KoBussLLC/grabert-hardware/PCB/grabert.kicad_sch

## KiCad design PCB/grabert.kicad_sch (2021-04-06)

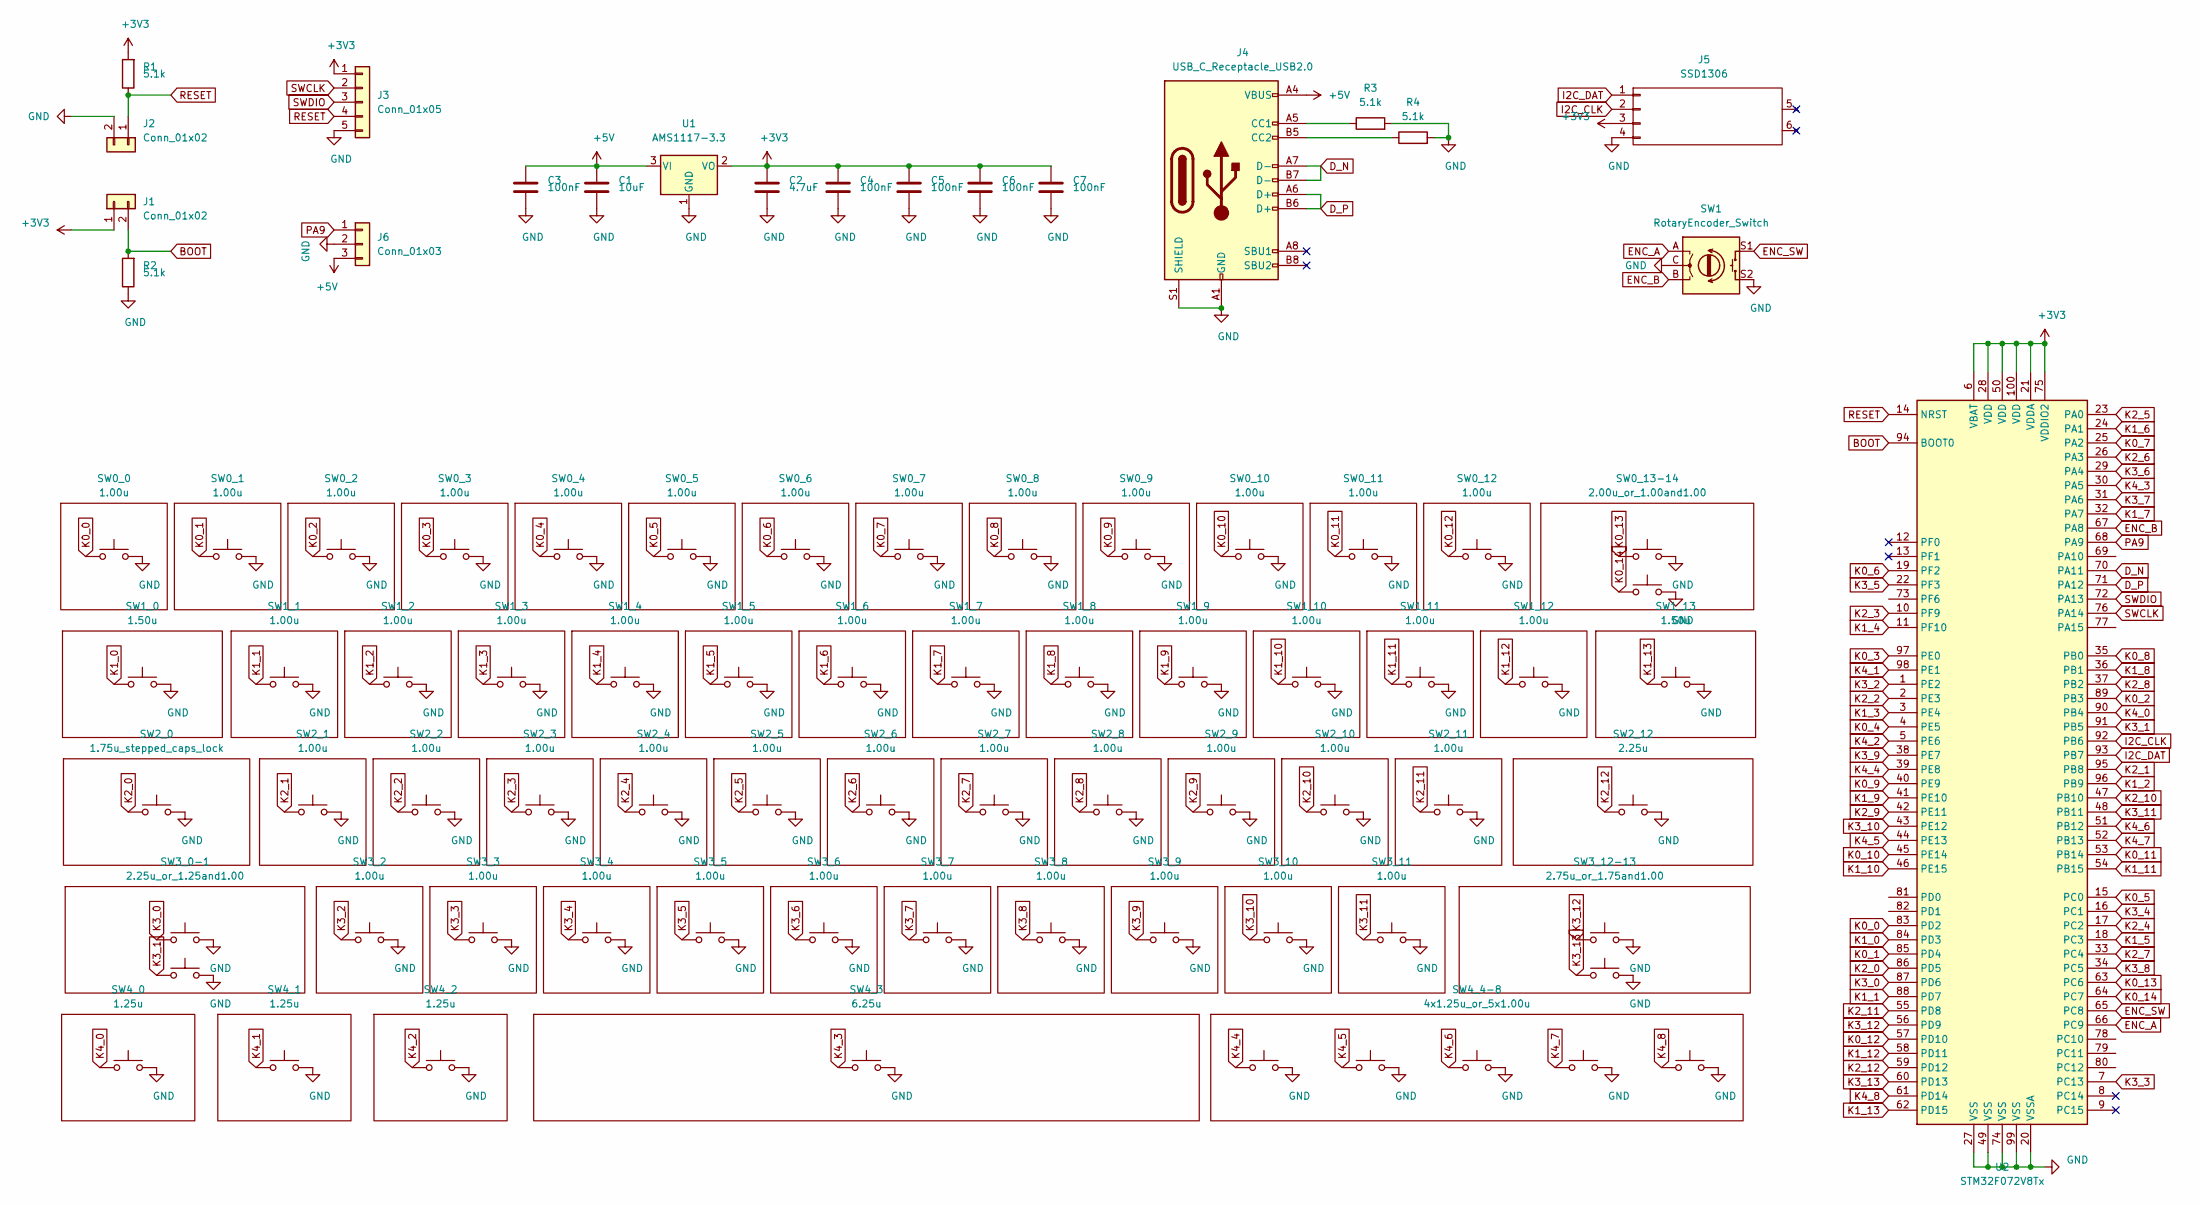
[picture p44: schematic grabert.kicad_sch]

Parts:
C1: 10uF; C_0603_1608Metric
C2: 4.7uF; C_0603_1608Metric
C3, C4, C5, C6, C7: 100nF; C_0603_1608Metric
J1, J2: Conn_01x02; PinHeader_1x02_P2.54mm_Vertical
J3: Conn_01x05; PinHeader_1x05_P2.54mm_Vertical
J4: USB_C_Receptacle_USB2.0; U262-161N-4BVC11
J5: SSD1306
J6: Conn_01x03; PinHeader_1x03_P2.54mm_Vertical
R1, R2, R3, R4: 5.1k; R_0603_1608Metric
SW0_0, SW0_1, SW0_2, SW0_3, SW0_4, SW0_5, SW0_6, SW0_7, SW0_8, SW0_9, SW0_10, SW0_11, SW0_12, SW1_1, SW1_2, SW1_3, SW1_4, SW1_5, SW1_6, SW1_7, SW1_8, SW1_9, SW1_10, SW1_11, SW1_12, SW2_1, SW2_2, SW2_3, SW2_4, SW2_5, SW2_6, SW2_7, SW2_8, SW2_9, SW2_10, SW2_11, SW3_2, SW3_3, SW3_4, SW3_5, SW3_6, SW3_7, SW3_8, SW3_9, SW3_10, SW3_11: 1.00u; MX_1u
SW0_13-14: 2.00u_or_1.00and1.00; MX_2.00u_or_1.00and1.00
SW1: RotaryEncoder_Switch; PEC11R-4220K-S0024
SW1_0, SW1_13: 1.50u; MX_1.50u
SW2_0: 1.75u_stepped_caps_lock; MX_1.75u_stepped_caps
SW2_12: 2.25u; MX_2.25u
SW3_0-1: 2.25u_or_1.25and1.00; MX_2.25u_or_1.25and1.00
SW3_12-13: 2.75u_or_1.75and1.00; MX_2.75u_or_1.75and1.00
SW4_0, SW4_1, SW4_2: 1.25u; MX_1.25
SW4_3: 6.25u; MX_6.25u
SW4_4-8: 4x1.25u_or_5x1.00u; MX_4x1.25u_or_5x1.00u
U1: AMS1117-3.3; SOT-223-3_TabPin2
U2: STM32F072V8Tx; LQFP-100_14x14mm_P0.5mm

Connections:
+3V3: C2.1, C4.1, C5.1, C6.1, C7.1, J1.1, J3.1, J5.3 (VCC), R1.2, U1.2 (VO), U2.6 (VBAT), U2.21 (VDDA), U2.28 (VDD), U2.50 (VDD), U2.75 (VDDIO2), U2.100 (VDD)
+5V: C1.1, C3.1, J4.A4 (VBUS), J4.A9 (VBUS), J4.B4 (VBUS), J4.B9 (VBUS), J6.3, U1.3 (VI)
BOOT: J1.2, R2.2, U2.94 (BOOT0)
D_N: J4.A7 (D-), J4.B7 (D-), U2.70 (PA11)
D_P: J4.A6 (D+), J4.B6 (D+), U2.71 (PA12)
ENC_A: SW1.A, U2.66 (PC9)
ENC_B: SW1.B, U2.67 (PA8)
ENC_SW: SW1.S1, U2.65 (PC8)
GND: C1.2, C2.2, C3.2, C4.2, C5.2, C6.2, C7.2, J2.2, J3.5, J4.A1 (GND), J4.A12 (GND), J4.B1 (GND), J4.B12 (GND), J4.S1 (SHIELD), J5.4 (GND), J6.2, R2.1, R3.2, R4.2, SW0_0.2, SW0_1.2, SW0_2.2, SW0_3.2, SW0_4.2, SW0_5.2, SW0_6.2, SW0_7.2, SW0_8.2, SW0_9.2, SW0_10.2, SW0_11.2, SW0_12.2, SW0_13-14.2, SW0_13-14.4, SW1.C, SW1.S2, SW1_0.2, SW1_1.2, SW1_2.2, SW1_3.2, SW1_4.2, SW1_5.2, SW1_6.2, SW1_7.2, SW1_8.2, SW1_9.2, SW1_10.2, SW1_11.2, SW1_12.2, SW1_13.2, SW2_0.2, SW2_1.2, SW2_2.2, SW2_3.2, SW2_4.2, SW2_5.2, SW2_6.2, SW2_7.2, SW2_8.2, SW2_9.2, SW2_10.2, SW2_11.2, SW2_12.2, SW3_0-1.2, SW3_0-1.4, SW3_2.2, SW3_3.2, SW3_4.2, SW3_5.2, SW3_6.2, SW3_7.2, SW3_8.2, SW3_9.2, SW3_10.2, SW3_11.2, SW3_12-13.2, SW3_12-13.4, SW4_0.2, SW4_1.2, SW4_2.2, SW4_3.2, SW4_4-8.2, SW4_4-8.4, SW4_4-8.6, SW4_4-8.8, SW4_4-8.10, U1.1 (GND), U2.20 (VSSA), U2.27 (VSS), U2.49 (VSS), U2.74 (VSS), U2.99 (VSS)
I2C_CLK: J5.2 (SCL), U2.92 (PB6)
I2C_DAT: J5.1 (SDA), U2.93 (PB7)
K0_0: SW0_0.1, U2.83 (PD2)
K0_1: SW0_1.1, U2.85 (PD4)
K0_2: SW0_2.1, U2.89 (PB3)
K0_3: SW0_3.1, U2.97 (PE0)
K0_4: SW0_4.1, U2.4 (PE5)
K0_5: SW0_5.1, U2.15 (PC0)
K0_6: SW0_6.1, U2.19 (PF2)
K0_7: SW0_7.1, U2.25 (PA2)
K0_8: SW0_8.1, U2.35 (PB0)
K0_9: SW0_9.1, U2.40 (PE9)
K0_10: SW0_10.1, U2.45 (PE14)
K0_11: SW0_11.1, U2.53 (PB14)
K0_12: SW0_12.1, U2.57 (PD10)
K0_13: SW0_13-14.1, U2.63 (PC6)
K0_14: SW0_13-14.3, U2.64 (PC7)
K1_0: SW1_0.1, U2.84 (PD3)
K1_1: SW1_1.1, U2.88 (PD7)
K1_2: SW1_2.1, U2.96 (PB9)
K1_3: SW1_3.1, U2.3 (PE4)
K1_4: SW1_4.1, U2.11 (PF10)
K1_5: SW1_5.1, U2.18 (PC3)
K1_6: SW1_6.1, U2.24 (PA1)
K1_7: SW1_7.1, U2.32 (PA7)
K1_8: SW1_8.1, U2.36 (PB1)
K1_9: SW1_9.1, U2.41 (PE10)
K1_10: SW1_10.1, U2.46 (PE15)
K1_11: SW1_11.1, U2.54 (PB15)
K1_12: SW1_12.1, U2.58 (PD11)
K1_13: SW1_13.1, U2.62 (PD15)
K2_0: SW2_0.1, U2.86 (PD5)
K2_1: SW2_1.1, U2.95 (PB8)
K2_2: SW2_2.1, U2.2 (PE3)
K2_3: SW2_3.1, U2.10 (PF9)
K2_4: SW2_4.1, U2.17 (PC2)
K2_5: SW2_5.1, U2.23 (PA0)
K2_6: SW2_6.1, U2.26 (PA3)
K2_7: SW2_7.1, U2.33 (PC4)
K2_8: SW2_8.1, U2.37 (PB2)
K2_9: SW2_9.1, U2.42 (PE11)
K2_10: SW2_10.1, U2.47 (PB10)
K2_11: SW2_11.1, U2.55 (PD8)
K2_12: SW2_12.1, U2.59 (PD12)
K3_0: SW3_0-1.1, U2.87 (PD6)
K3_1: SW3_0-1.3, U2.91 (PB5)
K3_2: SW3_2.1, U2.1 (PE2)
K3_3: SW3_3.1, U2.7 (PC13)
K3_4: SW3_4.1, U2.16 (PC1)
K3_5: SW3_5.1, U2.22 (PF3)
K3_6: SW3_6.1, U2.29 (PA4)
K3_7: SW3_7.1, U2.31 (PA6)
K3_8: SW3_8.1, U2.34 (PC5)
K3_9: SW3_9.1, U2.38 (PE7)
K3_10: SW3_10.1, U2.43 (PE12)
K3_11: SW3_11.1, U2.48 (PB11)
K3_12: SW3_12-13.1, U2.56 (PD9)
K3_13: SW3_12-13.3, U2.60 (PD13)
K4_0: SW4_0.1, U2.90 (PB4)
K4_1: SW4_1.1, U2.98 (PE1)
K4_2: SW4_2.1, U2.5 (PE6)
K4_3: SW4_3.1, U2.30 (PA5)
K4_4: SW4_4-8.1, U2.39 (PE8)
K4_5: SW4_4-8.3, U2.44 (PE13)
K4_6: SW4_4-8.5, U2.51 (PB12)
K4_7: SW4_4-8.7, U2.52 (PB13)
K4_8: SW4_4-8.9, U2.61 (PD14)
unnamed: J4.A5 (CC1), R3.1
unnamed: J4.B5 (CC2), R4.1
PA9: J6.1, U2.68 (PA9)
RESET: J2.1, J3.4, R1.1, U2.14 (NRST)
SWCLK: J3.2, U2.76 (PA14)
SWDIO: J3.3, U2.72 (PA13)
